TinyTapeout/tt-demo-pcb/doc/img/tt07-demoboard.jpg

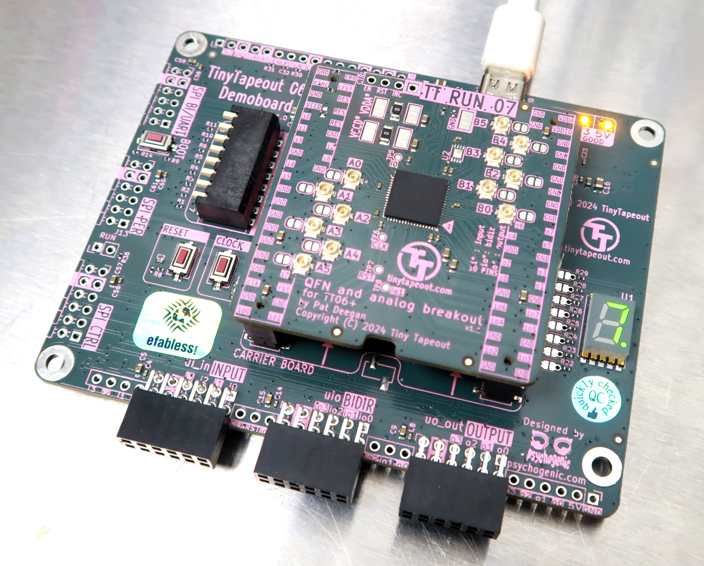
doc/img/tt07-demoboard.jpg
