TinyTapeout/tt-demo-pcb/rp2040.kicad_sch

## KiCad design rp2040.kicad_sch (2025-02-25)

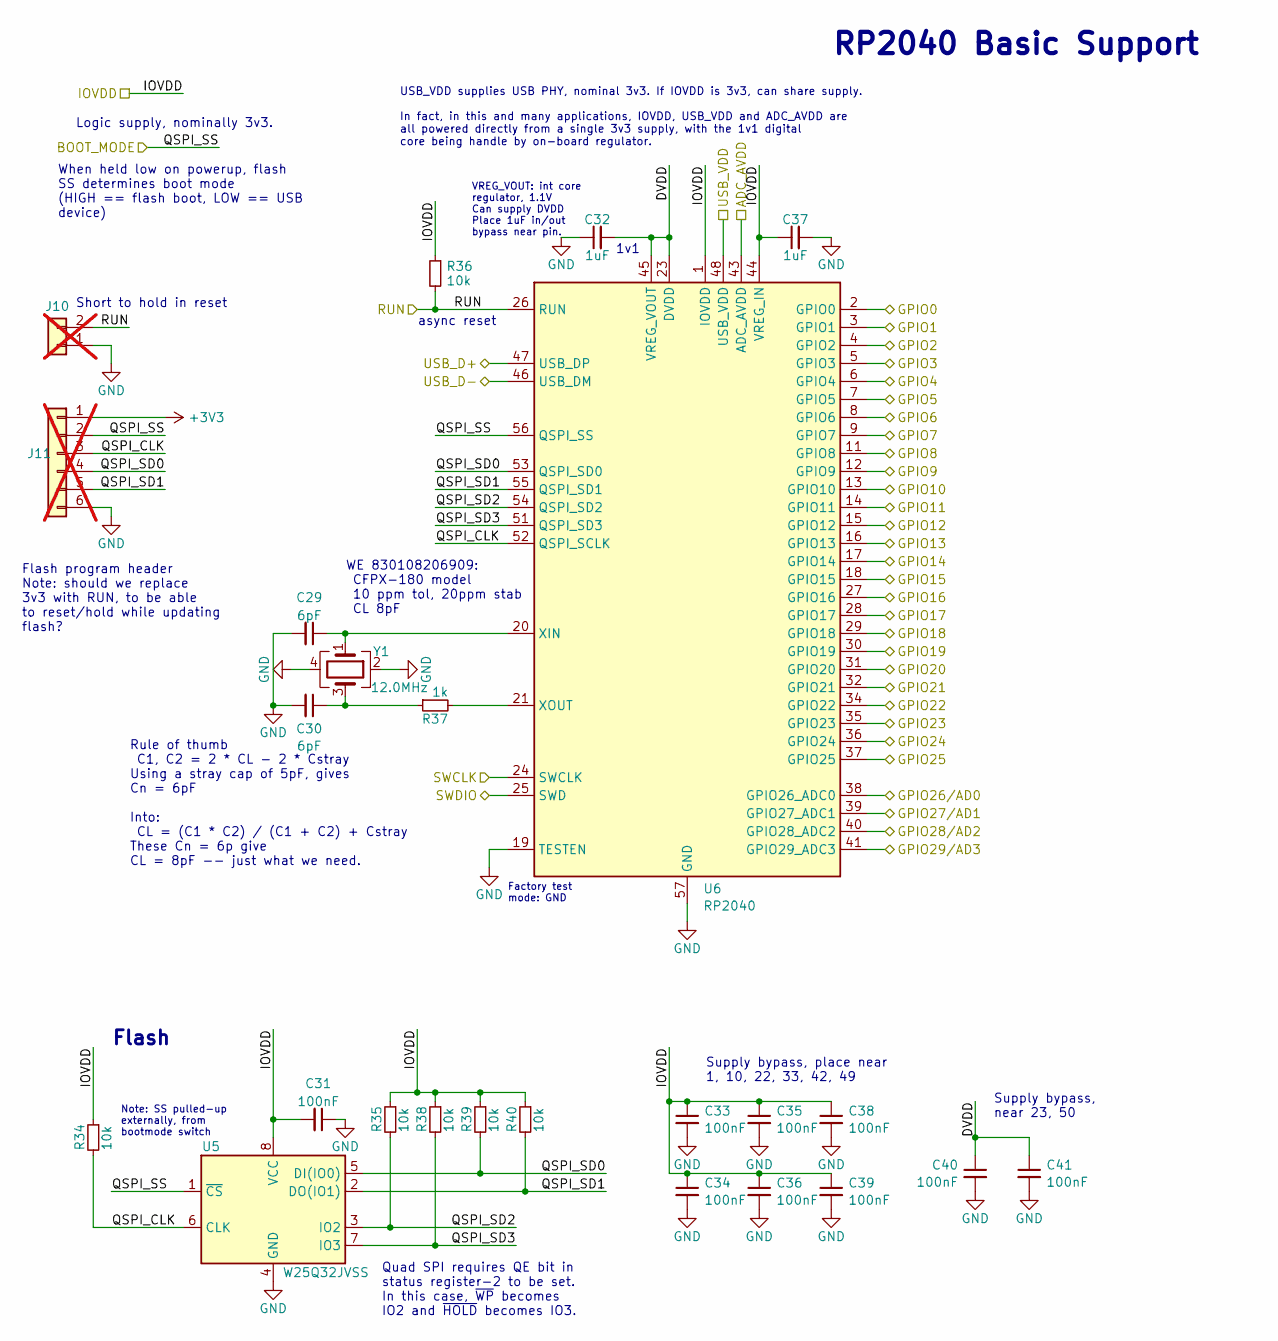
[picture p34: schematic rp2040.kicad_sch]

Parts:
C29, C30: 6pF; C_0402_1005Metric; MPN CC0402BRNPO9BN6R0; LCSC C541341
C31, C33, C34, C35, C36, C38, C39, C40, C41: 100nF; C_0402_1005Metric; MPN CL05A104KA5NNNC; LCSC C100072
C32, C37: 1uF; C_0603_1608Metric; MPN CL10A105KA8NNNC; LCSC C5673
J10: Conn_01x02; PinHeader_1x02_P2.54mm_Vertical; not fitted
J11: Conn_01x06; PinHeader_1x06_P2.54mm_Vertical_SMD_Pin1Right; MPN 61300611121; not fitted
R34, R35, R36, R38, R39, R40: 10k; R_0402_1005Metric; MPN RC0402FR-0710KL; LCSC C471764
R37: 1k; R_0402_1005Metric; MPN CR0402-FX-1001GLF; LCSC C202394
U5: W25Q32JVSS; SOIC-8_5.23x5.23mm_P1.27mm; MPN W25Q32JVSSIQ; DigikeyPN W25Q32JVSSIQ-ND
U6: RP2040; QFN-56-1EP_7x7mm_P0.4mm_EP3.2x3.2mm; MPN SC0914(13); DigikeyPN 2648-SC0914(13)CT-ND
Y1: 12.0MHz; Crystal_SMD_3225-4Pin_3.2x2.5mm; MPN 830108206909; DigikeyPN 1923-830108206909DKR-ND

Connections:
+3V3: J11.1
ADC_AVDD: U6.43 (ADC_AVDD)
BOOT_MODE: J11.2, U5.1 (~CS), U6.56 (QSPI_SS)
DVDD: C32.2, C40.1, C41.1, U6.23 (DVDD), U6.45 (VREG_VOUT), U6.50 (DVDD)
GND: C29.2, C30.2, C31.1, C32.1, C33.2, C34.2, C35.2, C36.2, C37.2, C38.2, C39.2, C40.2, C41.2, J10.1, J11.6, U5.4 (GND), U6.19 (TESTEN), U6.57 (GND), Y1.2, Y1.4
GPIO0: U6.2 (GPIO0)
GPIO1: U6.3 (GPIO1)
GPIO2: U6.4 (GPIO2)
GPIO3: U6.5 (GPIO3)
GPIO4: U6.6 (GPIO4)
GPIO5: U6.7 (GPIO5)
GPIO6: U6.8 (GPIO6)
GPIO7: U6.9 (GPIO7)
GPIO8: U6.11 (GPIO8)
GPIO9: U6.12 (GPIO9)
GPIO10: U6.13 (GPIO10)
GPIO11: U6.14 (GPIO11)
GPIO12: U6.15 (GPIO12)
GPIO13: U6.16 (GPIO13)
GPIO14: U6.17 (GPIO14)
GPIO15: U6.18 (GPIO15)
GPIO16: U6.27 (GPIO16)
GPIO17: U6.28 (GPIO17)
GPIO18: U6.29 (GPIO18)
GPIO19: U6.30 (GPIO19)
GPIO20: U6.31 (GPIO20)
GPIO21: U6.32 (GPIO21)
GPIO22: U6.34 (GPIO22)
GPIO23: U6.35 (GPIO23)
GPIO24: U6.36 (GPIO24)
GPIO25: U6.37 (GPIO25)
GPIO26/AD0: U6.38 (GPIO26_ADC0)
GPIO27/AD1: U6.39 (GPIO27_ADC1)
GPIO28/AD2: U6.40 (GPIO28_ADC2)
GPIO29/AD3: U6.41 (GPIO29_ADC3)
IOVDD: C31.2, C33.1, C34.1, C35.1, C36.1, C37.1, C38.1, C39.1, R34.1, R35.1, R36.1, R38.1, R39.1, R40.1, U5.8 (VCC), U6.1 (IOVDD), U6.10 (IOVDD), U6.22 (IOVDD), U6.33 (IOVDD), U6.42 (IOVDD), U6.44 (VREG_IN), U6.49 (IOVDD)
unnamed: C29.1, U6.20 (XIN), Y1.1
unnamed: C30.1, R37.1, Y1.3
unnamed: R37.2, U6.21 (XOUT)
QSPI_CLK: J11.3, R34.2, U5.6 (CLK), U6.52 (QSPI_SCLK)
QSPI_SD0: J11.4, R39.2, U5.5 (DI(IO0)), U6.53 (QSPI_SD0)
QSPI_SD1: J11.5, R40.2, U5.2 (DO(IO1)), U6.55 (QSPI_SD1)
QSPI_SD2: R35.2, U5.3 (IO2), U6.54 (QSPI_SD2)
QSPI_SD3: R38.2, U5.7 (IO3), U6.51 (QSPI_SD3)
RUN: J10.2, R36.2, U6.26 (RUN)
SWCLK: U6.24 (SWCLK)
SWDIO: U6.25 (SWD)
USB_D+: U6.47 (USB_DP)
USB_D-: U6.46 (USB_DM)
USB_VDD: U6.48 (USB_VDD)

Notes on the sheet:
async reset
RP2040 Basic Support
Flash
Short to hold in reset
VREG_VOUT: int core regulator, 1.1V Can supply DVDD Place 1uF in/out bypass near pin.
When held low on powerup, flash SS determines boot mode (HIGH == flash boot, LOW == USB device)
WE 830108206909: CFPX-180 model 10 ppm tol, 20ppm stab CL 8pF
1v1
USB_VDD supplies USB PHY, nominal 3v3. If IOVDD is 3v3, can share supply. In fact, in this and many applications, IOVDD, USB_VDD and ADC_AVDD are all powered directly from a single 3v3 supply, with the 1v1 digital core being handle by on-board regulator.
Flash program header Note: should we replace 3v3 with RUN, to be able to reset/hold while updating flash?
Supply bypass, place near 1, 10, 22, 33, 42, 49
Quad SPI requires QE bit in status register-2 to be set. In this case, ~{WP} becomes IO2 and ~{HOLD} becomes IO3.
Factory test mode: GND
Rule of thumb C1, C2 = 2 * CL - 2 * Cstray Using a stray cap of 5pF, gives Cn = 6pF Into: CL = (C1 * C2) / (C1 + C2) + Cstray These Cn = 6p give CL = 8pF -- just what we need.
Logic supply, nominally 3v3.
Supply bypass, near 23, 50
Note: SS pulled-up externally, from bootmode switch
