TinyTapeout/tt-demo-pcb/rp2350.kicad_sch

## KiCad design rp2350.kicad_sch (2026-06-23)

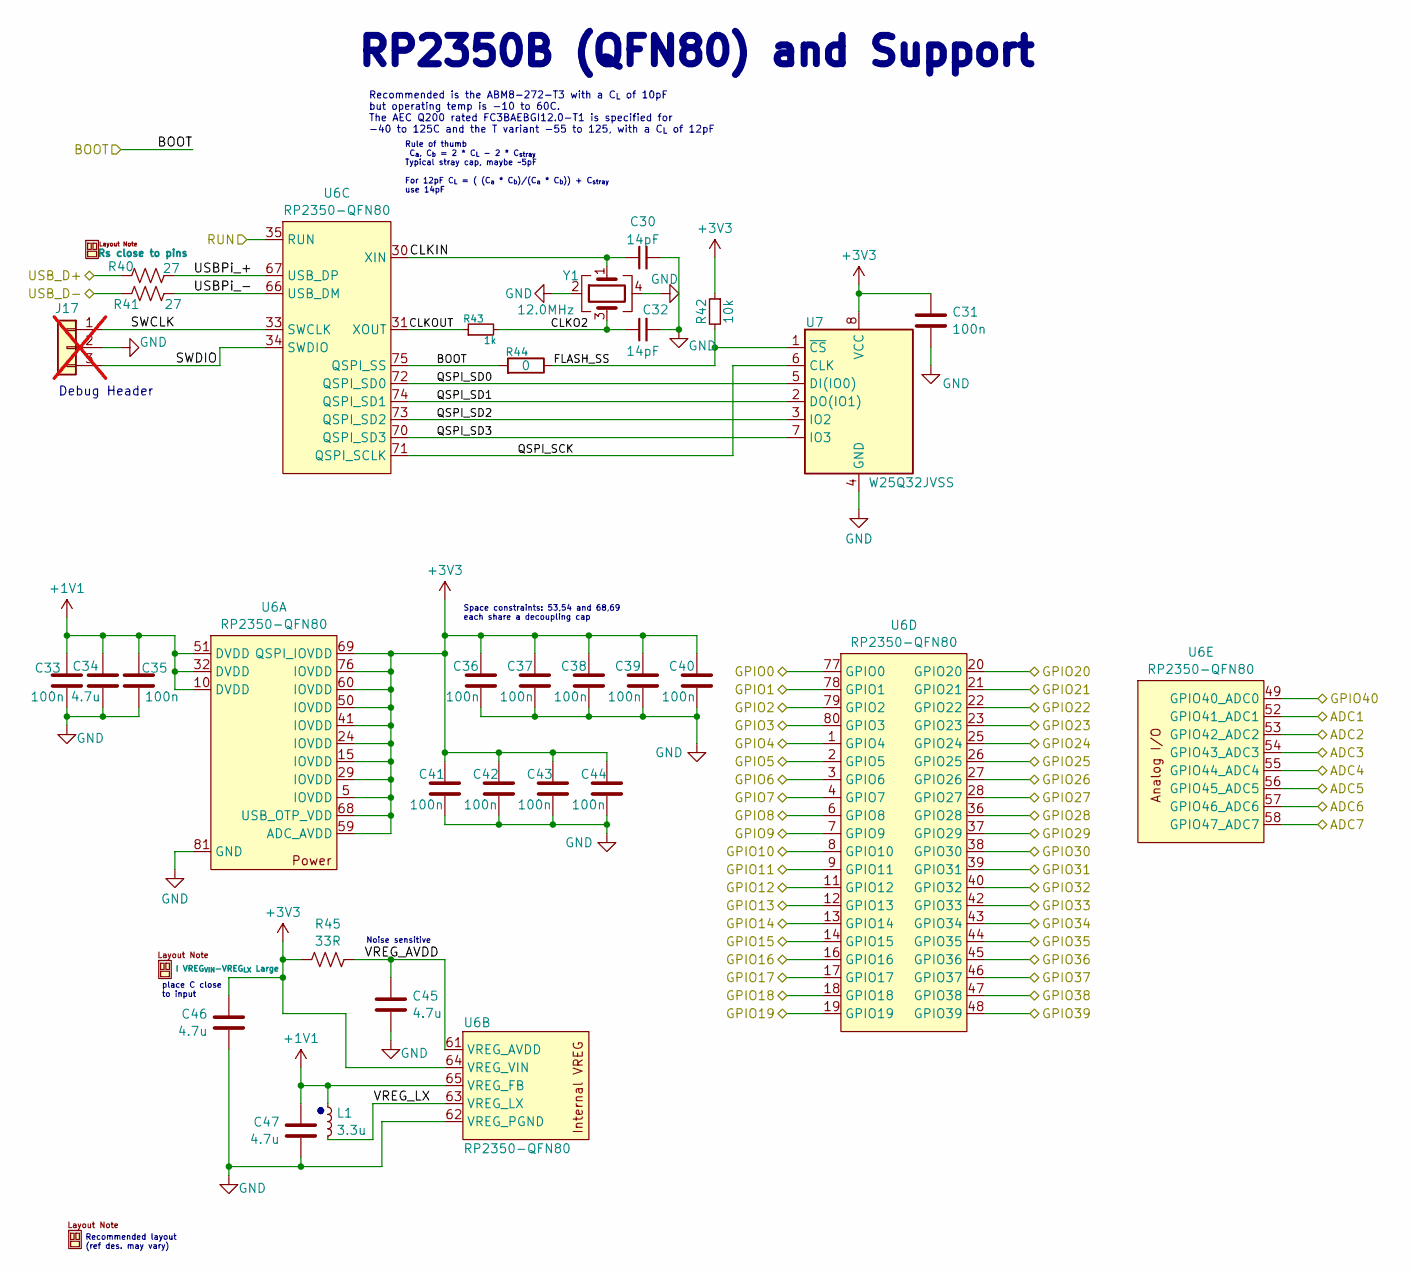
[picture p35: schematic rp2350.kicad_sch]

Parts:
C30, C32: 14pF; C_0402_1005Metric; MPN CC0402CRNPO9BN4R0; LCSC C325455
C31, C33, C35, C36, C37, C38, C39, C40, C41, C42, C43, C44: 100n; C_0402_1005Metric; MPN CL05A104KA5NNNC; LCSC C100072
C34, C45: 4.7u; C_0402_1005Metric; MPN GRM155R61E475ME15D; JLC C2858031
C46, C47: 4.7u; C_0603_1608Metric; MPN GRM188C71C475KE21D; JLC C237615
J17: Conn_01x03; PinHeader_1x03_P2.54mm_Vertical; not fitted
L1: 3.3u; L_2016X120N; MPN AOTA-B201610S3R3-101-T; DigikeyPN 535-AOTA-B201610S3R3-101-TCT-ND
LAYOUT1: Rs close to pins
LAYOUT2: I VREG_{VIN}-VREG_{LX} Large
LAYOUT3: (no value)
R40, R41: 27; R_0402_1005Metric; MPN AF0402FR-0727RL; JLC C2098172
R42: 10k; R_0402_1005Metric; MPN RC0402FR-0710KL; LCSC C471764
R43: 1k; R_0402_1005Metric; MPN CR0402-FX-1001GLF; LCSC C202394
R44: 0; R_0402_1005Metric; MPN RMCF0402ZT0R00; DigikeyPN RMCF0402ZT0R00CT-ND
R45: 33R; R_0402_1005Metric; MPN RCS040233R0FKED; JLC C25105
U6: RP2350-QFN80; QFN-80-1EP_10x10mm_P0.4mm_EP3.4x3.4mm; MPN RP2350B; JLC C42415655
U7: W25Q32JVSS; SOIC-8_5.3x5.3mm_P1.27mm; MPN W25Q32JVSSIQ; JLC C82344
Y1: 12.0MHz; Crystal_SMD_3225-4Pin_3.2x2.5mm; MPN FC3BAEBGI12.0-T1; DigikeyPN 631-FC3BAEBGI12.0-T1CT-ND

Connections:
+1V1: C33.1, C34.1, C35.1, C47.1, L1.1, U6.10 (DVDD), U6.32 (DVDD), U6.51 (DVDD), U6.65 (VREG_FB)
+3V3: C31.1, C36.1, C37.1, C38.1, C39.1, C40.1, C41.1, C42.1, C43.1, C44.1, C46.1, R42.1, R45.1, U6.5 (IOVDD), U6.15 (IOVDD), U6.24 (IOVDD), U6.29 (IOVDD), U6.41 (IOVDD), U6.50 (IOVDD), U6.59 (ADC_AVDD), U6.60 (IOVDD), U6.64 (VREG_VIN), U6.68 (USB_OTP_VDD), U6.69 (QSPI_IOVDD), U6.76 (IOVDD), U7.8 (VCC)
ADC1: U6.52 (GPIO41_ADC1)
ADC2: U6.53 (GPIO42_ADC2)
ADC3: U6.54 (GPIO43_ADC3)
ADC4: U6.55 (GPIO44_ADC4)
ADC5: U6.56 (GPIO45_ADC5)
ADC6: U6.57 (GPIO46_ADC6)
ADC7: U6.58 (GPIO47_ADC7)
BOOT: R44.1, U6.75 (QSPI_SS)
CLKIN: C30.1, U6.30 (XIN), Y1.1
CLKO2: C32.1, R43.2, Y1.3
CLKOUT: R43.1, U6.31 (XOUT)
FLASH_SS: R42.2, R44.2, U7.1 (~CS)
GND: C30.2, C31.2, C32.2, C33.2, C34.2, C35.2, C36.2, C37.2, C38.2, C39.2, C40.2, C41.2, C42.2, C43.2, C44.2, C45.2, C46.2, C47.2, J17.2, U6.62 (VREG_PGND), U6.81 (GND), U7.4 (GND), Y1.2, Y1.4
GPIO0: U6.77 (GPIO0)
GPIO1: U6.78 (GPIO1)
GPIO2: U6.79 (GPIO2)
GPIO3: U6.80 (GPIO3)
GPIO4: U6.1 (GPIO4)
GPIO5: U6.2 (GPIO5)
GPIO6: U6.3 (GPIO6)
GPIO7: U6.4 (GPIO7)
GPIO8: U6.6 (GPIO8)
GPIO9: U6.7 (GPIO9)
GPIO10: U6.8 (GPIO10)
GPIO11: U6.9 (GPIO11)
GPIO12: U6.11 (GPIO12)
GPIO13: U6.12 (GPIO13)
GPIO14: U6.13 (GPIO14)
GPIO15: U6.14 (GPIO15)
GPIO16: U6.16 (GPIO16)
GPIO17: U6.17 (GPIO17)
GPIO18: U6.18 (GPIO18)
GPIO19: U6.19 (GPIO19)
GPIO20: U6.20 (GPIO20)
GPIO21: U6.21 (GPIO21)
GPIO22: U6.22 (GPIO22)
GPIO23: U6.23 (GPIO23)
GPIO24: U6.25 (GPIO24)
GPIO25: U6.26 (GPIO25)
GPIO26: U6.27 (GPIO26)
GPIO27: U6.28 (GPIO27)
GPIO28: U6.36 (GPIO28)
GPIO29: U6.37 (GPIO29)
GPIO30: U6.38 (GPIO30)
GPIO31: U6.39 (GPIO31)
GPIO32: U6.40 (GPIO32)
GPIO33: U6.42 (GPIO33)
GPIO34: U6.43 (GPIO34)
GPIO35: U6.44 (GPIO35)
GPIO36: U6.45 (GPIO36)
GPIO37: U6.46 (GPIO37)
GPIO38: U6.47 (GPIO38)
GPIO39: U6.48 (GPIO39)
GPIO40: U6.49 (GPIO40_ADC0)
QSPI_SCK: U6.71 (QSPI_SCLK), U7.6 (CLK)
QSPI_SD0: U6.72 (QSPI_SD0), U7.5 (DI(IO0))
QSPI_SD1: U6.74 (QSPI_SD1), U7.2 (DO(IO1))
QSPI_SD2: U6.73 (QSPI_SD2), U7.3 (IO2)
QSPI_SD3: U6.70 (QSPI_SD3), U7.7 (IO3)
RUN: U6.35 (RUN)
SWCLK: J17.1, U6.33 (SWCLK)
SWDIO: J17.3, U6.34 (SWDIO)
USBPi_+: R40.2, U6.67 (USB_DP)
USBPi_-: R41.2, U6.66 (USB_DM)
USB_D+: R40.1
USB_D-: R41.1
VREG_AVDD: C45.1, R45.2, U6.61 (VREG_AVDD)
VREG_LX: L1.2, U6.63 (VREG_LX)

Notes on the sheet:
Debug Header
Space constraints: 53,54 and 68,69 each share a decoupling cap
place C close to input
Noise sensitive
RP2350B (QFN80) and Support
Rule of thumb C_{a}, C_{b} = 2 * C_{L} - 2 * C_{stray} Typical stray cap, maybe ~5pF For 12pF C_{L} = ( (C_{a} * C_{b})/(C_{a} * C_{b})) + C_{stray} use 14pF
Recommended layout (ref des. may vary)
Recommended is the ABM8-272-T3 with a C_{L} of 10pF but operating temp is -10 to 60C. The AEC Q200 rated FC3BAEBGI12.0-T1 is specified for -40 to 125C and the T variant -55 to 125, with a C_{L} of 12pF
